kysilv/z80-rp2350b-zx-compatible/hardware/1_schematic.png

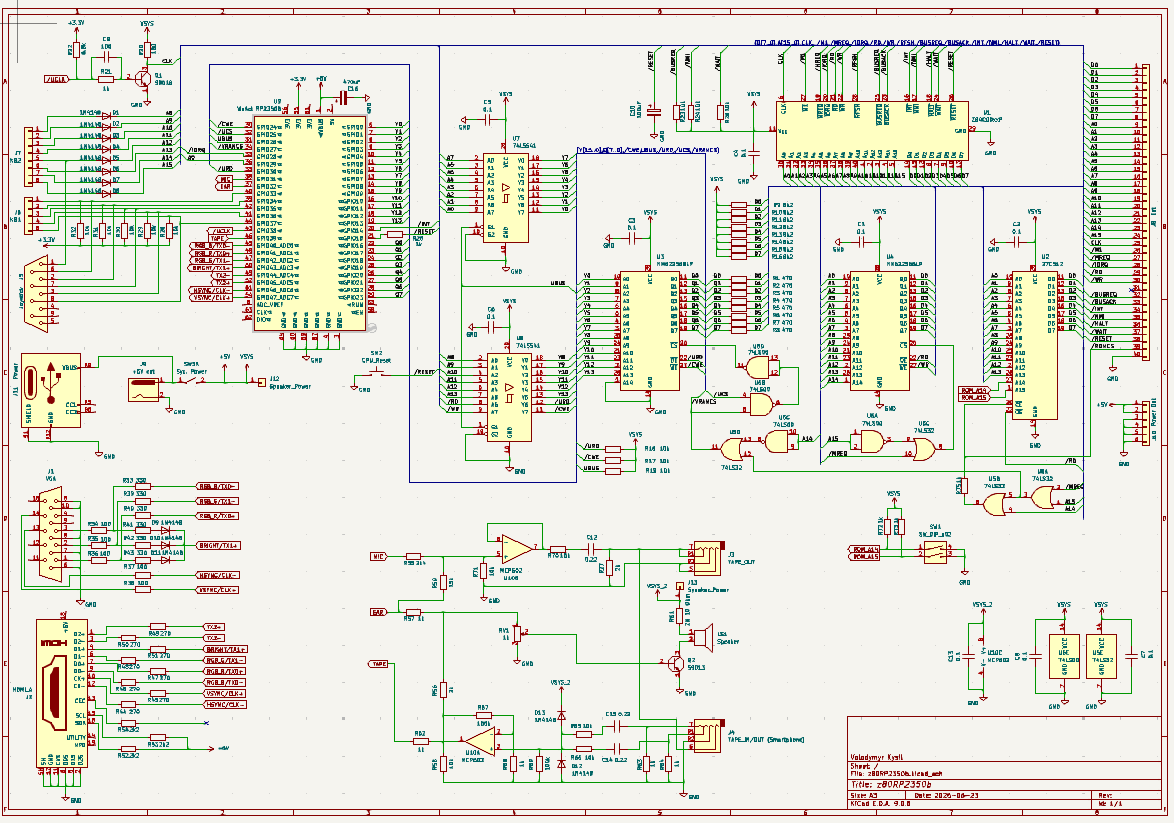
hardware/1_schematic.png
