kysilv/z80-rp2350b-zx-compatible/hardware/2_pcb_front.jpg

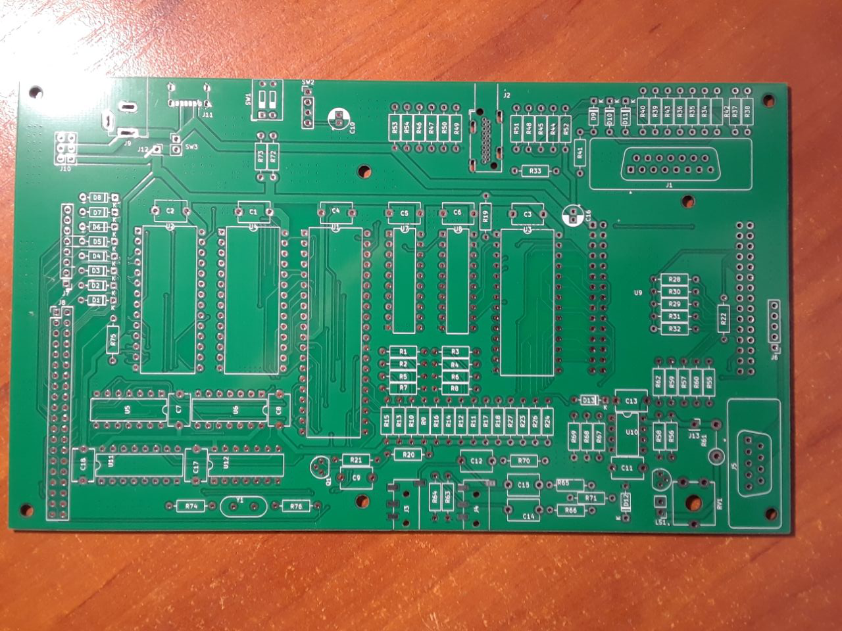
hardware/2_pcb_front.jpg
