kysilv/z80-rp2350b-zx-compatible/hardware/3_pcb_back.jpg

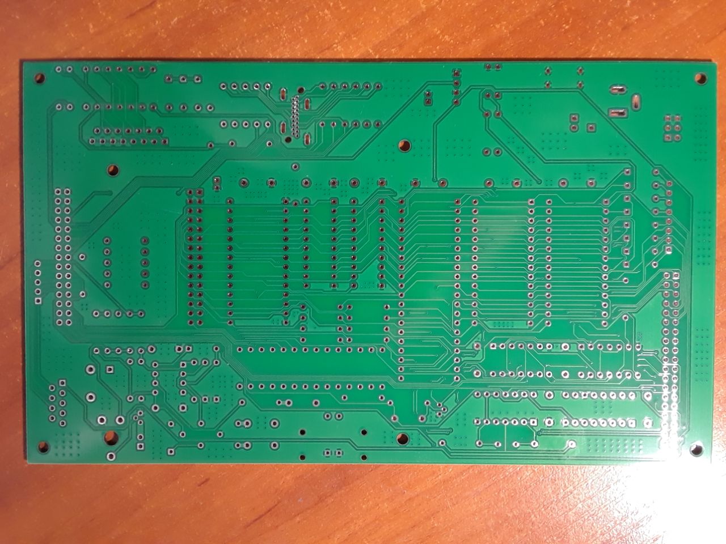
hardware/3_pcb_back.jpg
