kysilv/z80-rp2350b-zx-compatible/hardware/5_HDMI_Schematic.png

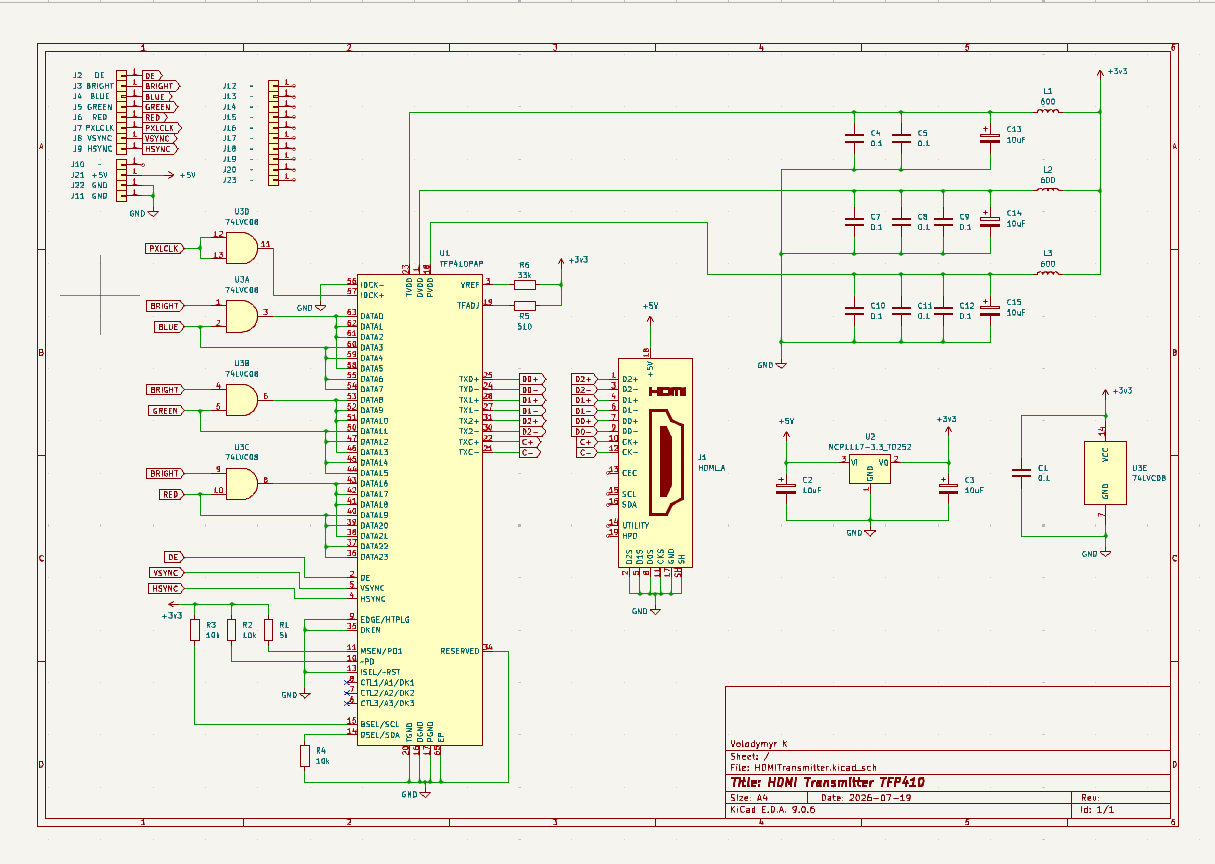
hardware/5_HDMI_Schematic.png
