kysilv/z80-rp2350b-zx-compatible/hardware/6_HDMI_pcb.png

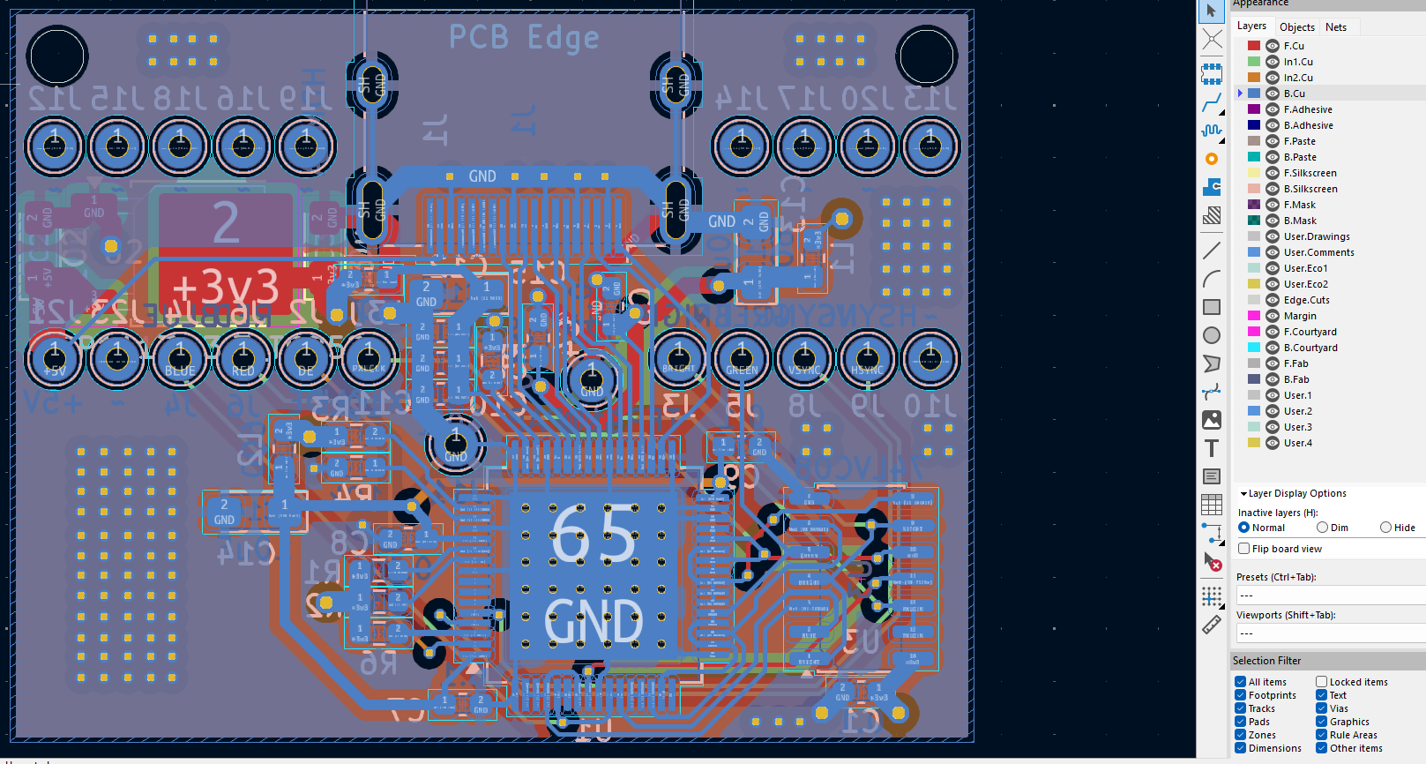
hardware/6_HDMI_pcb.png
