kysilv/z80-rp2350b-zx-compatible/photos/1_pcb.jpg

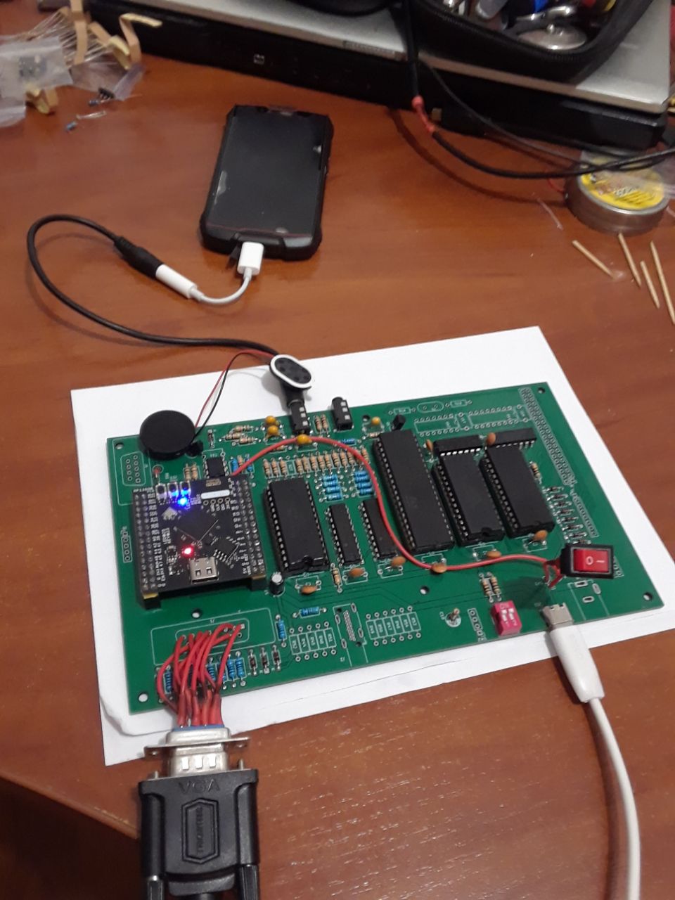
photos/1_pcb.jpg
