kysilv/z80-rp2350b-zx-compatible/photos/2_pcb_f.jpg

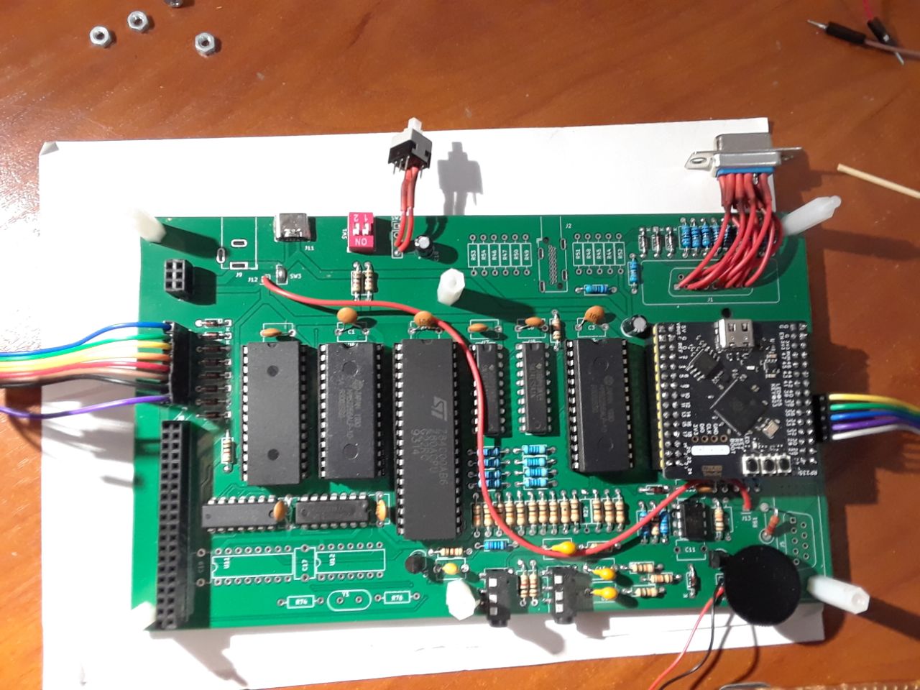
photos/2_pcb_f.jpg
