kysilv/z80-rp2350b-zx-compatible/photos/3_pcb_b.jpg

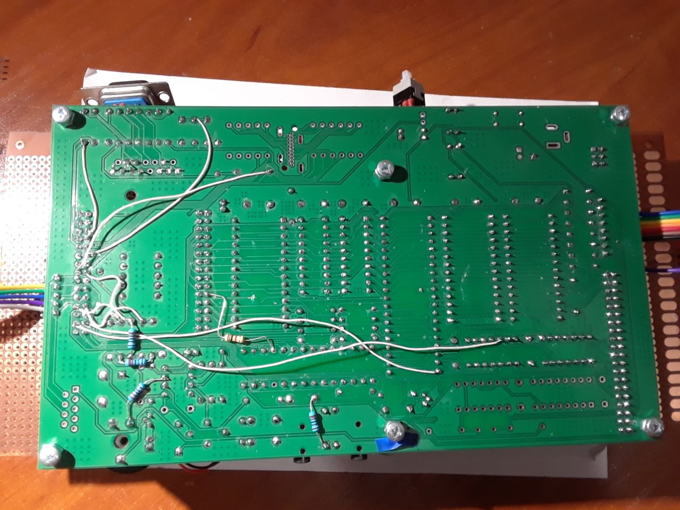
photos/3_pcb_b.jpg
