kysilv/z80-rp2350b-zx-compatible/photos/4_keyboard0_5.jpg

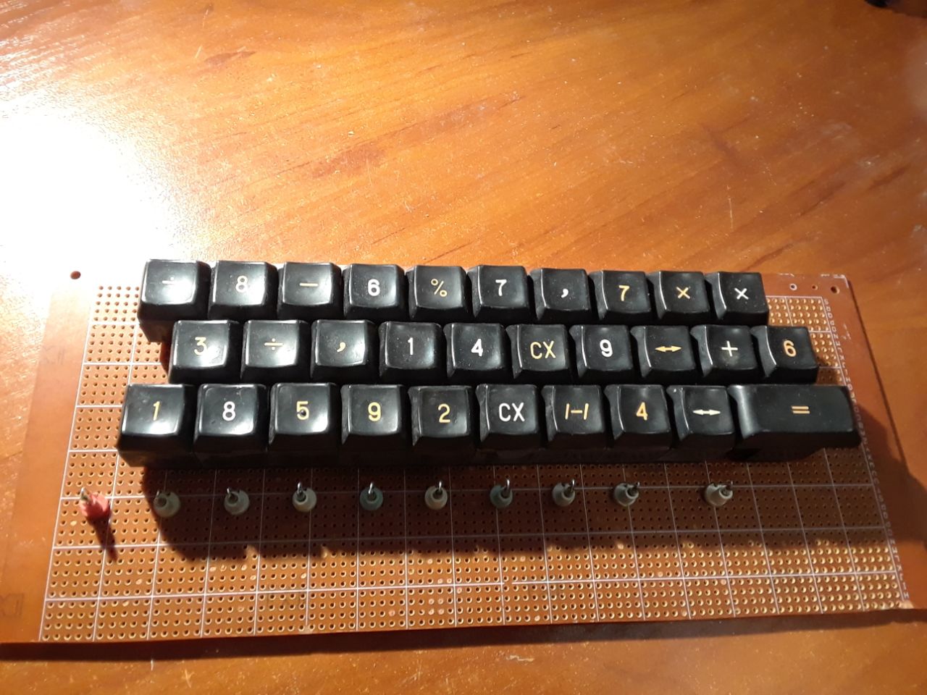
photos/4_keyboard0_5.jpg
