kysilv/z80-rp2350b-zx-compatible/photos/4_keyboard1.png

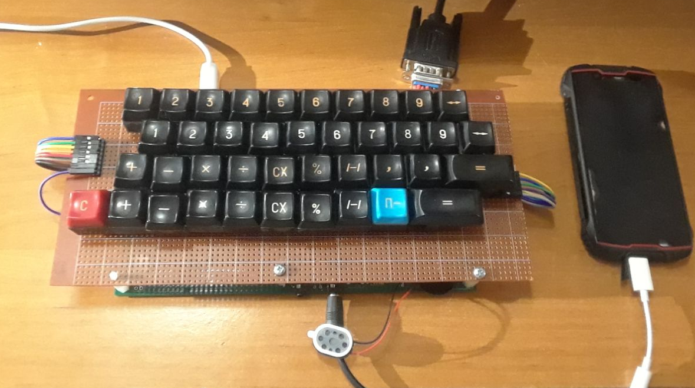
photos/4_keyboard1.png
