kysilv/z80-rp2350b-zx-compatible/photos/4_keyboard2.jpg

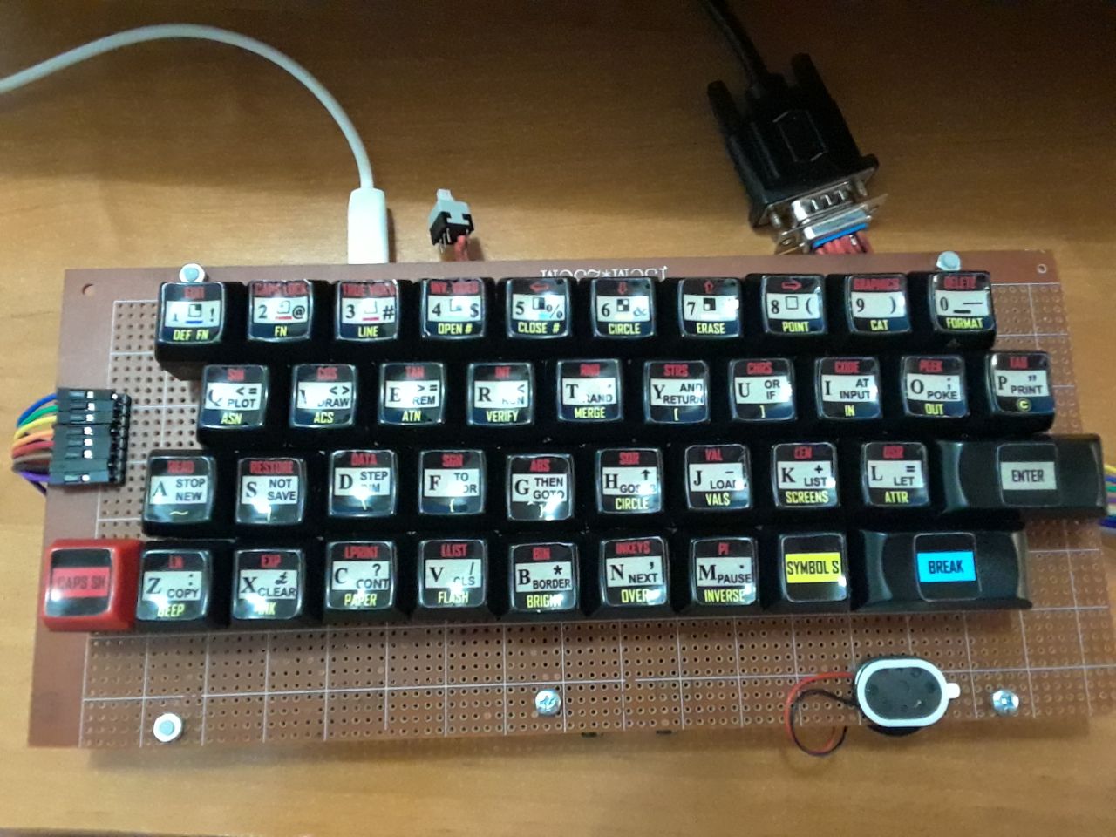
photos/4_keyboard2.jpg
