kysilv/z80-rp2350b-zx-compatible/photos/6_cancan.jpg

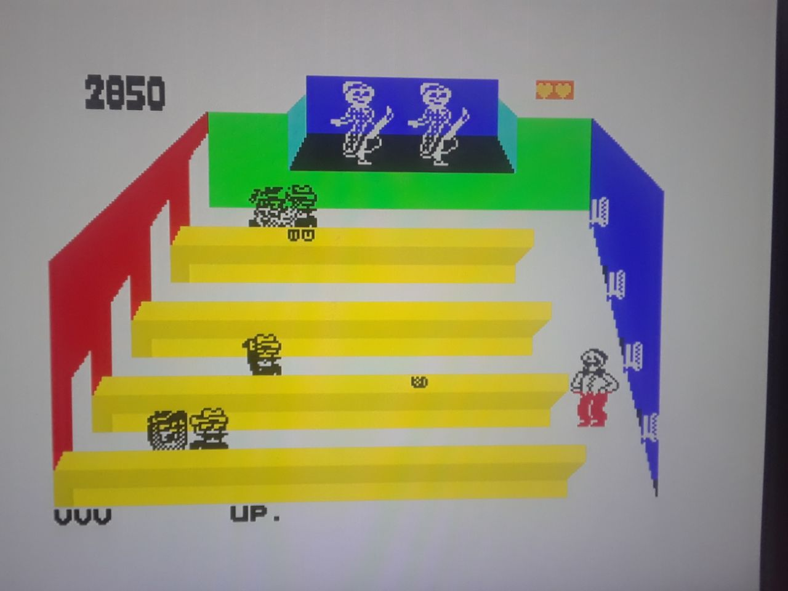
photos/6_cancan.jpg
