kysilv/z80-rp2350b-zx-compatible/photos/7_pepsi.jpg

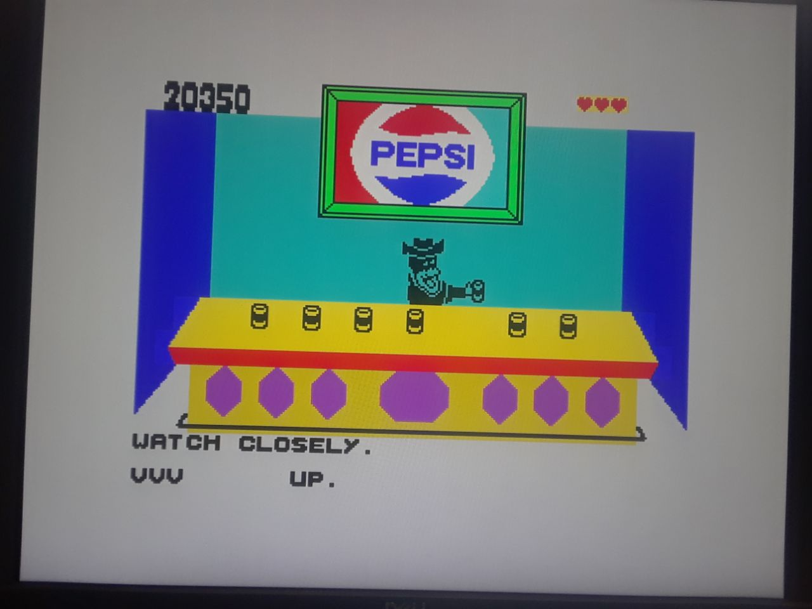
photos/7_pepsi.jpg
