kysilv/z80-rp2350b-zx-compatible/photos/barbarian.jpg

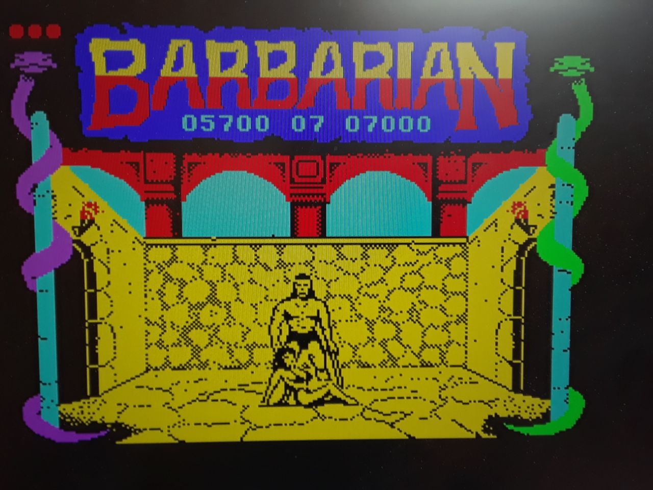
photos/barbarian.jpg
