kysilv/z80-rp2350b-zx-compatible/photos/elite.png

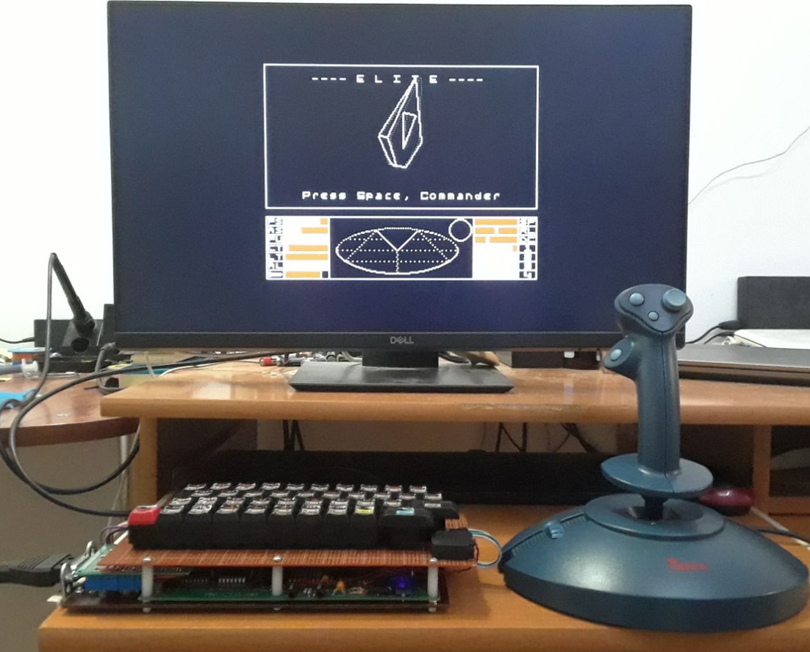
photos/elite.png
