kysilv/z80-rp2350b-zx-compatible/photos/joystick.jpg

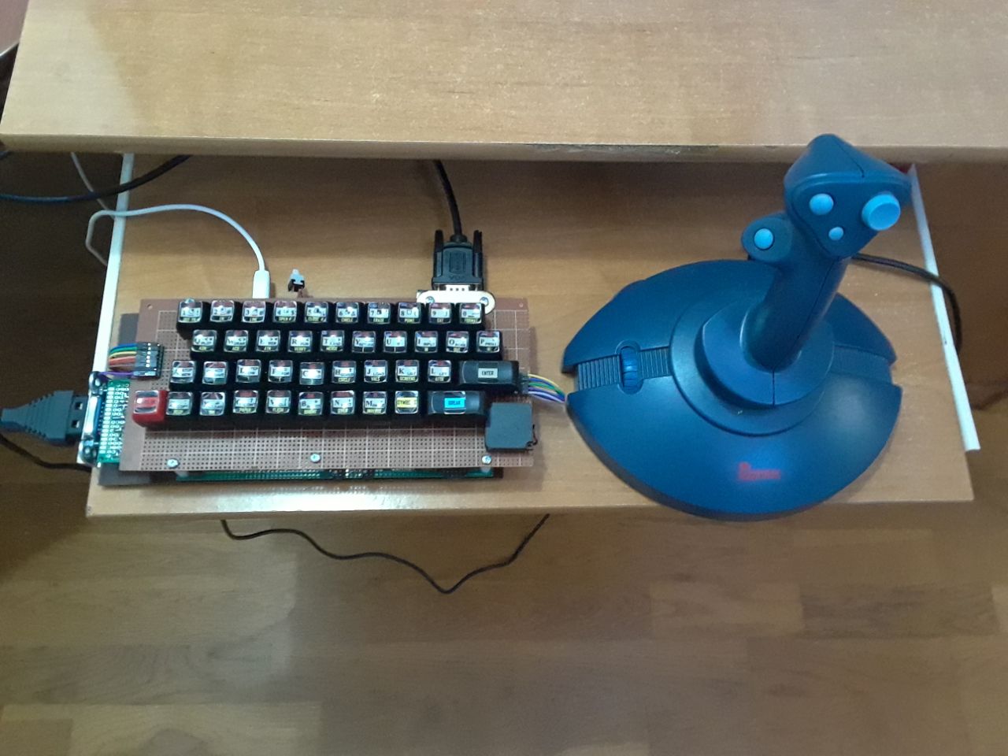
photos/joystick.jpg
