kysilv/z80-rp2350b-zx-compatible/photos/manic.jpg

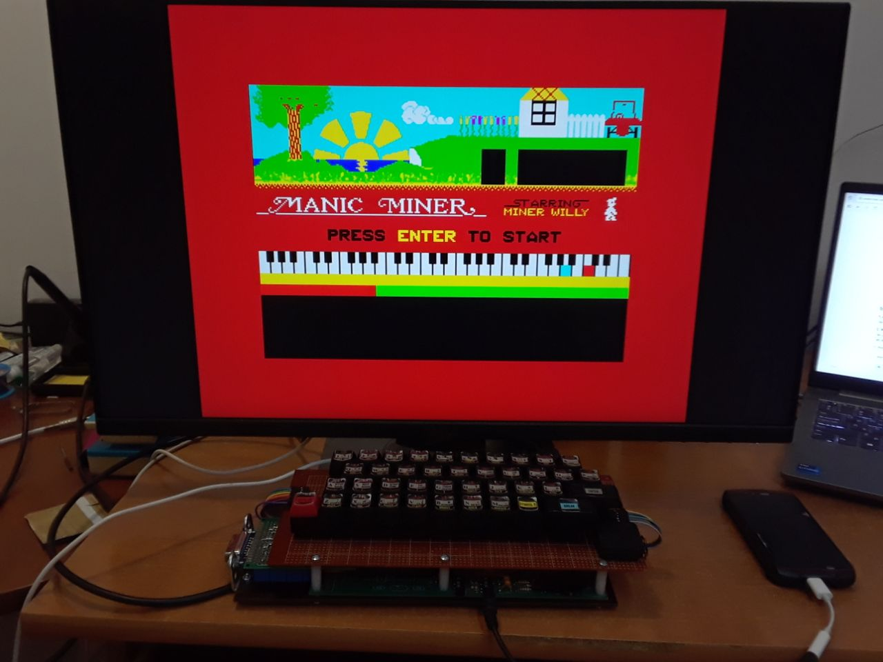
photos/manic.jpg
