kysilv/z80-rp2350b-zx-compatible/photos/palette.jpg

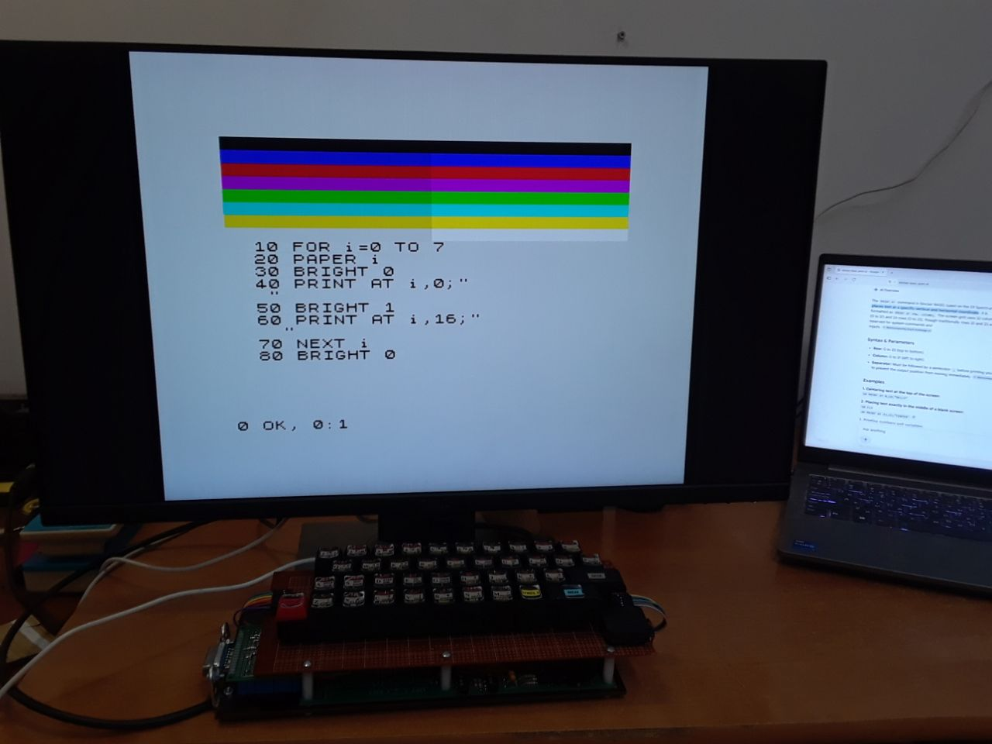
photos/palette.jpg
