kysilv/z80-rp2350b-zx-compatible/hardware/6_HDMI_soldered_board.jpg

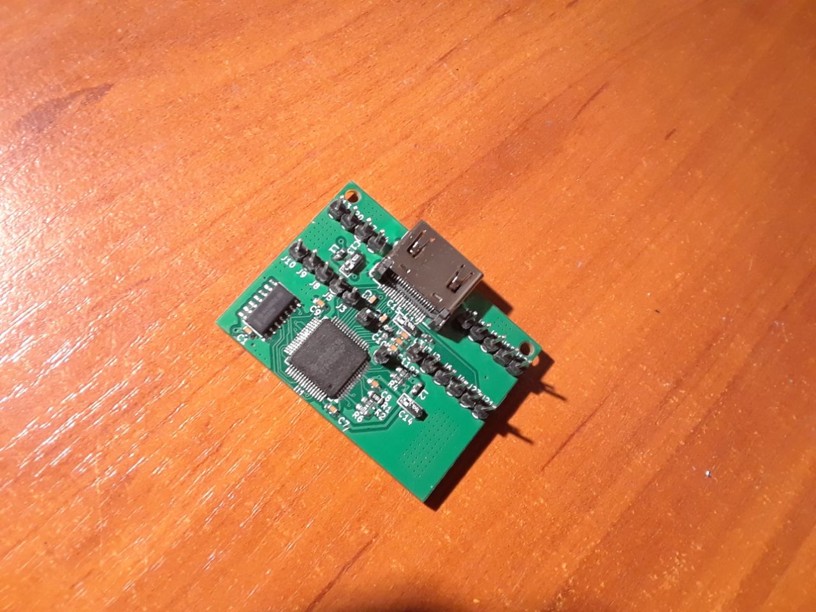
hardware/6_HDMI_soldered_board.jpg
