kysilv/z80-rp2350b-zx-compatible/hardware/9_HDMI_installed.jpg

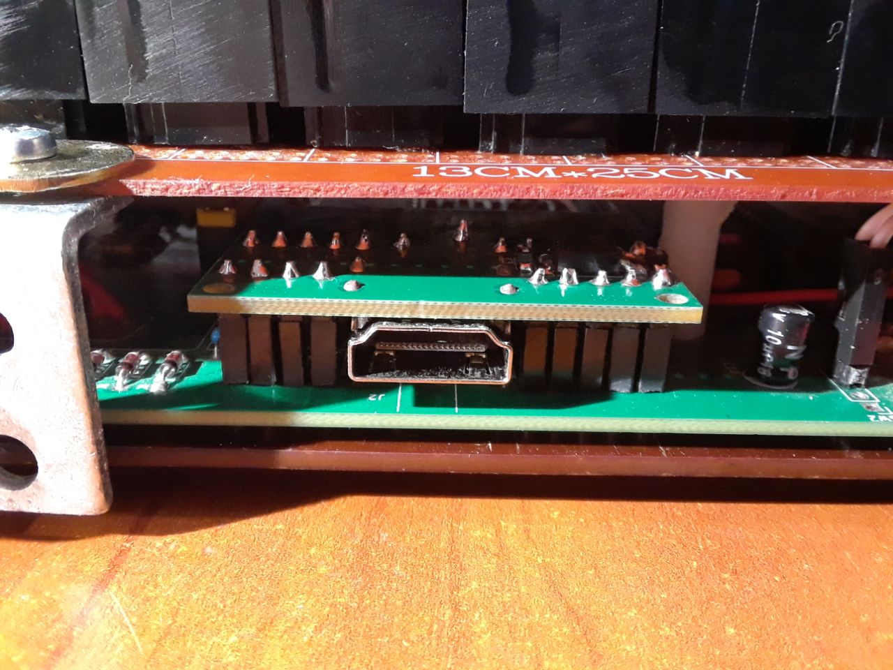
hardware/9_HDMI_installed.jpg
