kysilv/z80-rp2350b-zx-compatible/hardware/8_HDMI_test.jpg

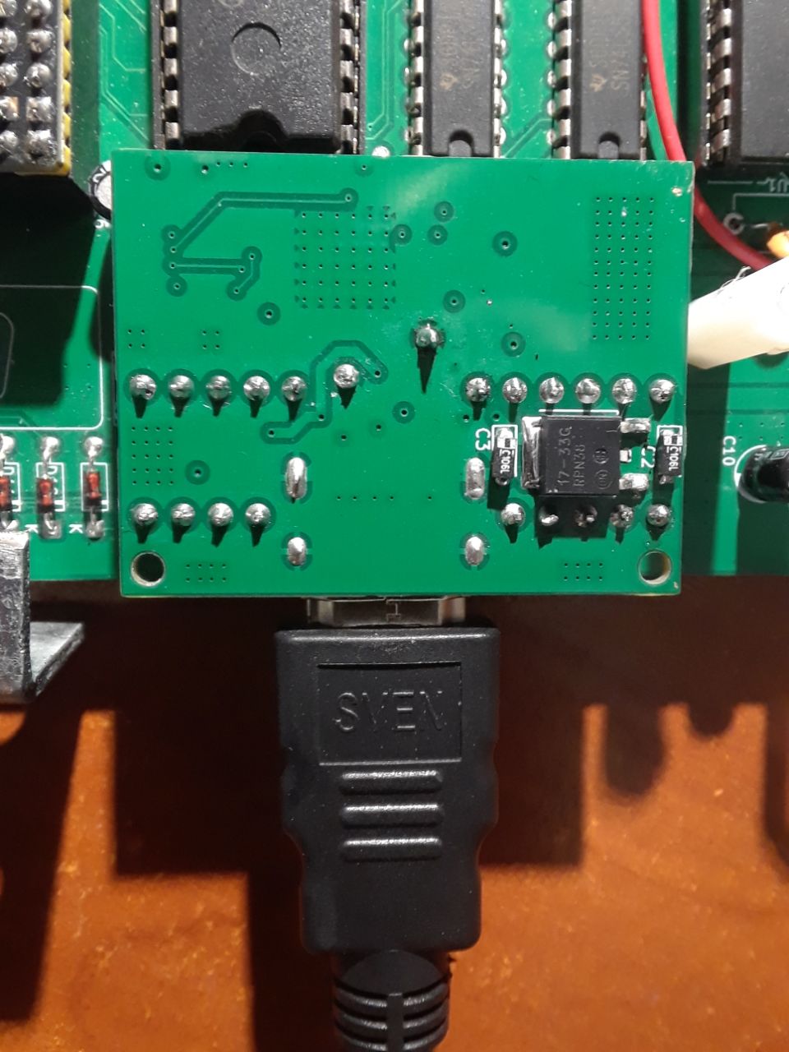
hardware/8_HDMI_test.jpg
