kysilv/z80-rp2350b-zx-compatible/photos/8_joystick_da15_tuning.jpg

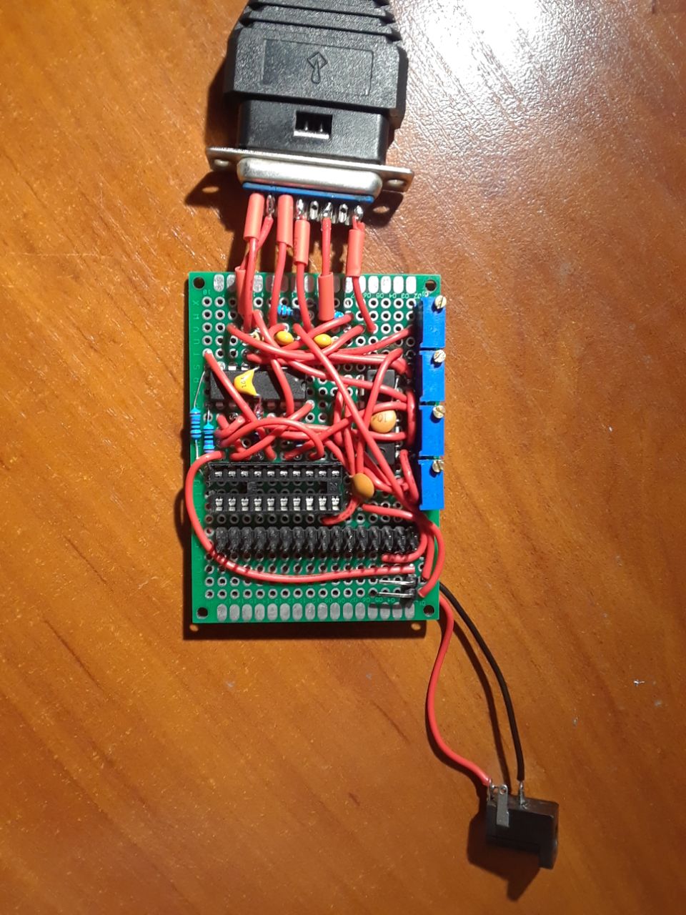
photos/8_joystick_da15_tuning.jpg
